MangoIV/dracuLad/graphics/marceline.png

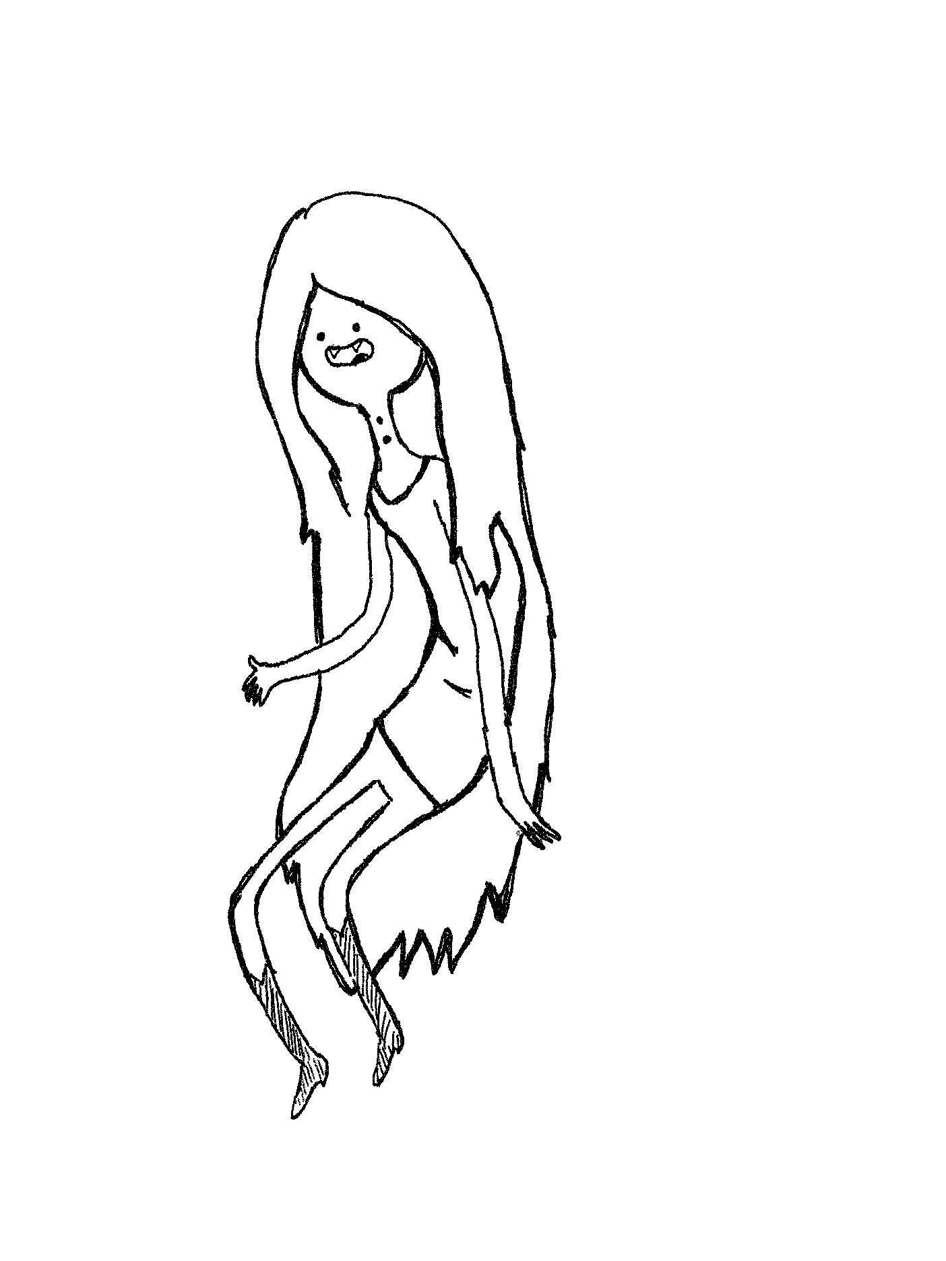
graphics/marceline.png
