MangoIV/dracuLad/pictures/rev2/acryli_no_caps_top.jpeg

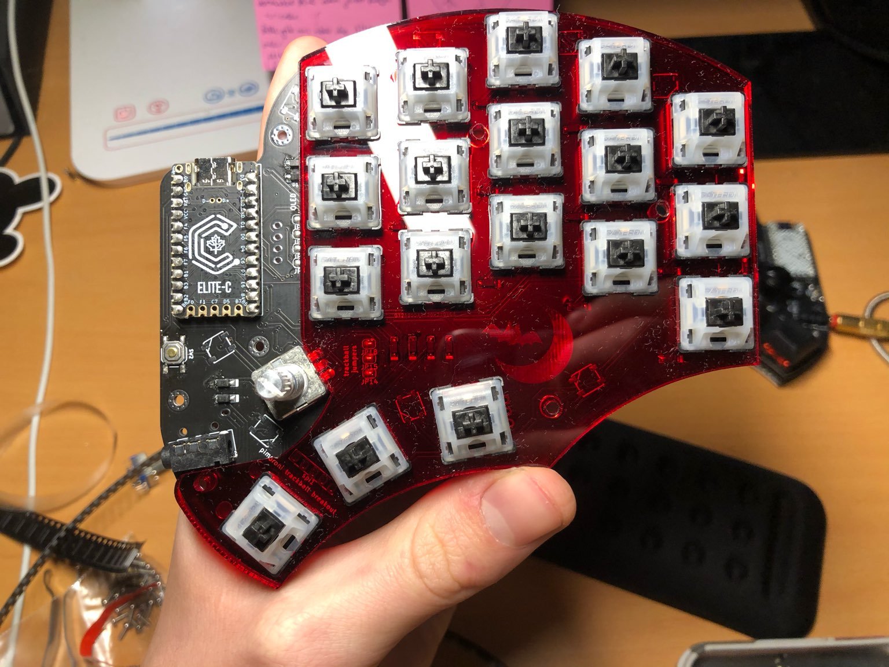
pictures/rev2/acryli_no_caps_top.jpeg
