MangoIV/dracuLad/pictures/rev2/acrylic_7mm_spacers.jpeg

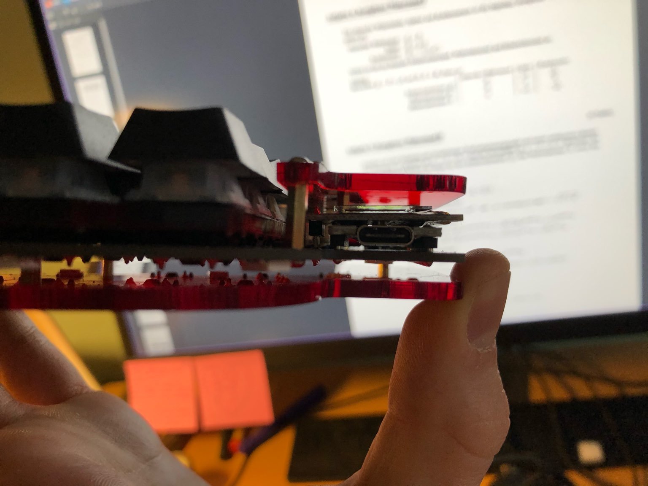
pictures/rev2/acrylic_7mm_spacers.jpeg
