MangoIV/dracuLad/pictures/rev2/acrylic_bottom_both_halves.jpeg

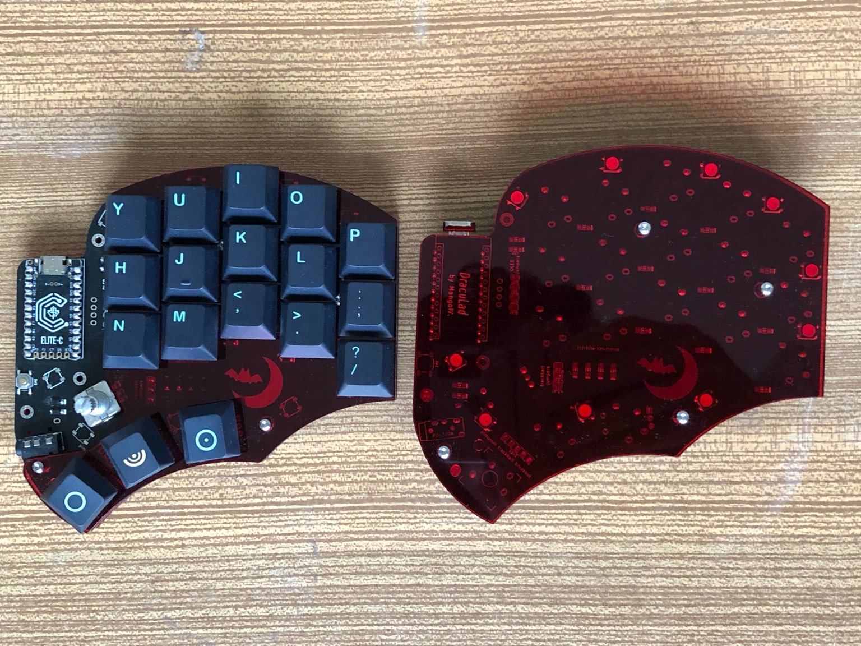
pictures/rev2/acrylic_bottom_both_halves.jpeg
