MangoIV/dracuLad/pictures/rev2/arylic_top_plate.jpeg

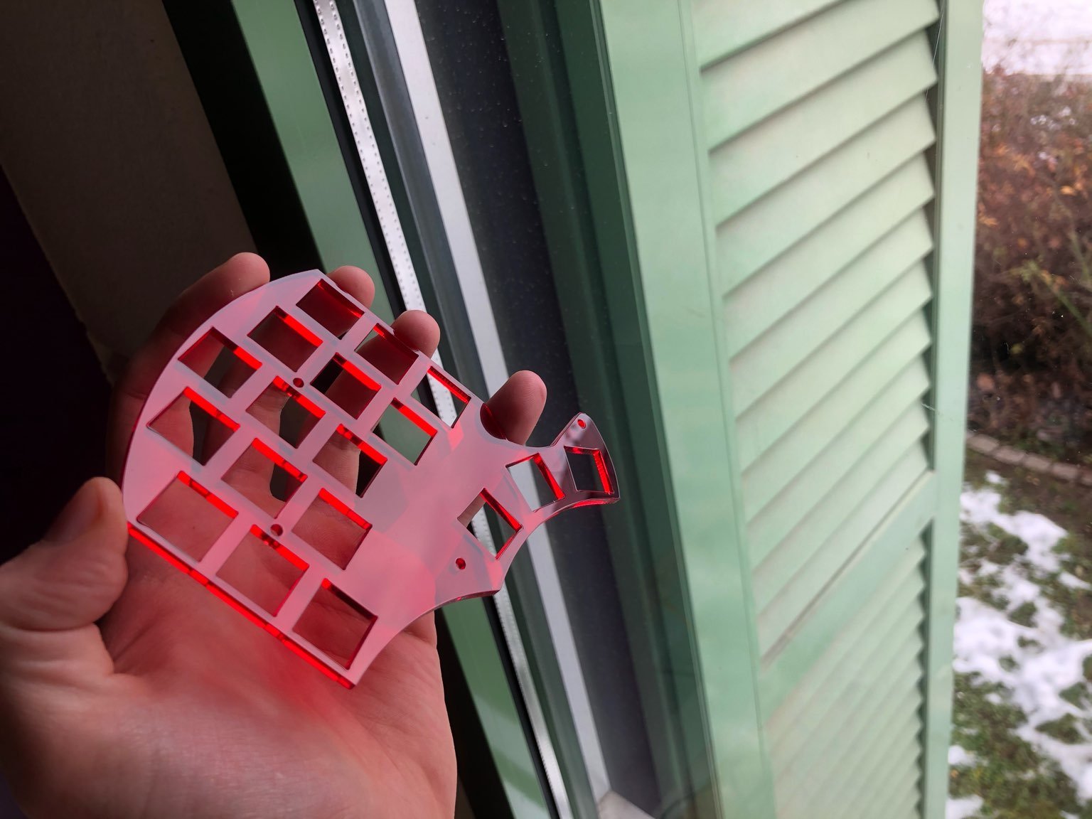
pictures/rev2/arylic_top_plate.jpeg
