MangoIV/dracuLad/pictures/rev2/fr4_glamour_puchi_c.jpeg

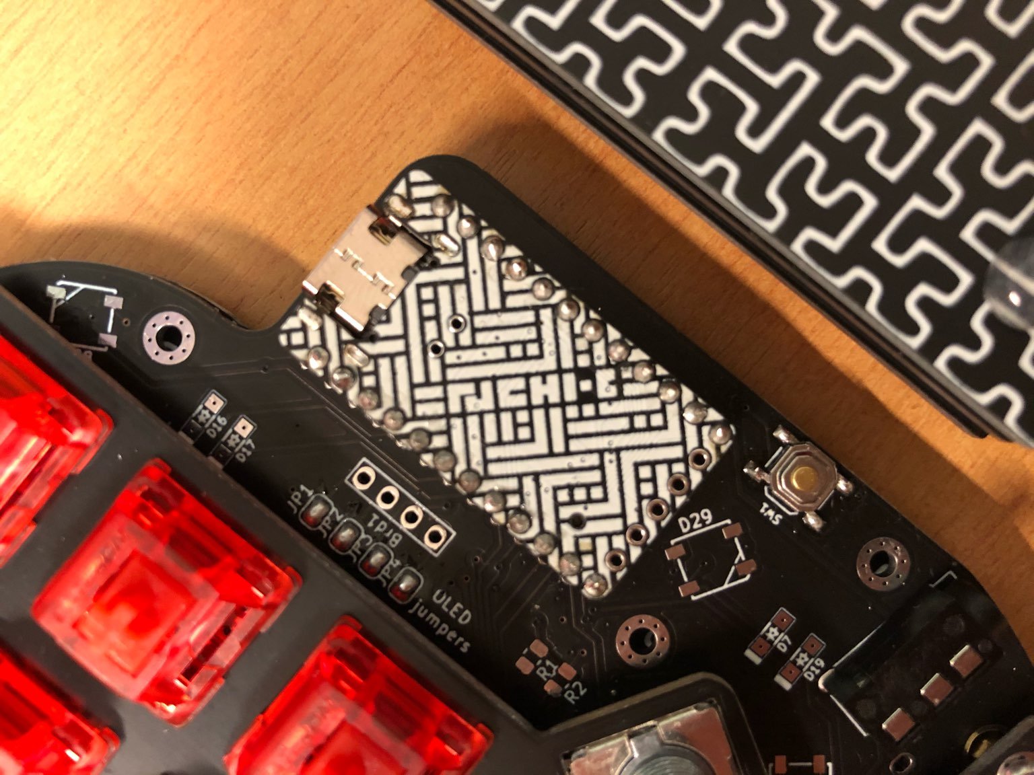
pictures/rev2/fr4_glamour_puchi_c.jpeg
