MangoIV/dracuLad/pictures/rev2/fr4_leds.jpeg

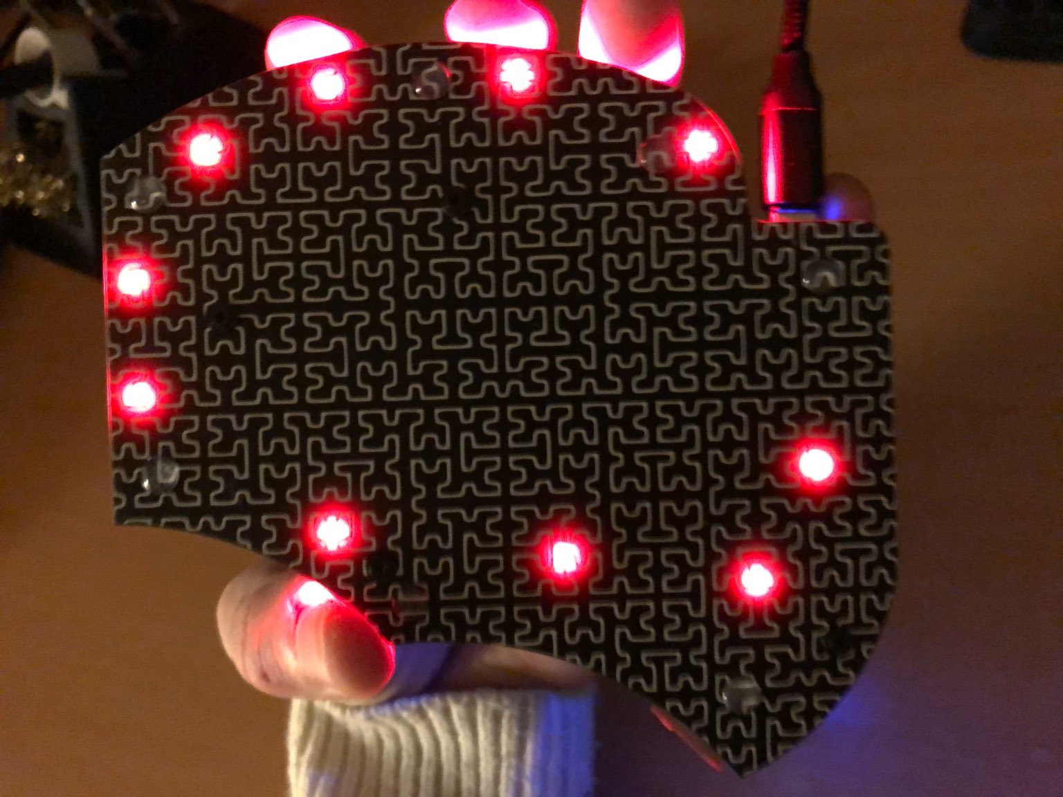
pictures/rev2/fr4_leds.jpeg
