MangoIV/dracuLad/pictures/rev2/fr4_mustard_packet.jpeg

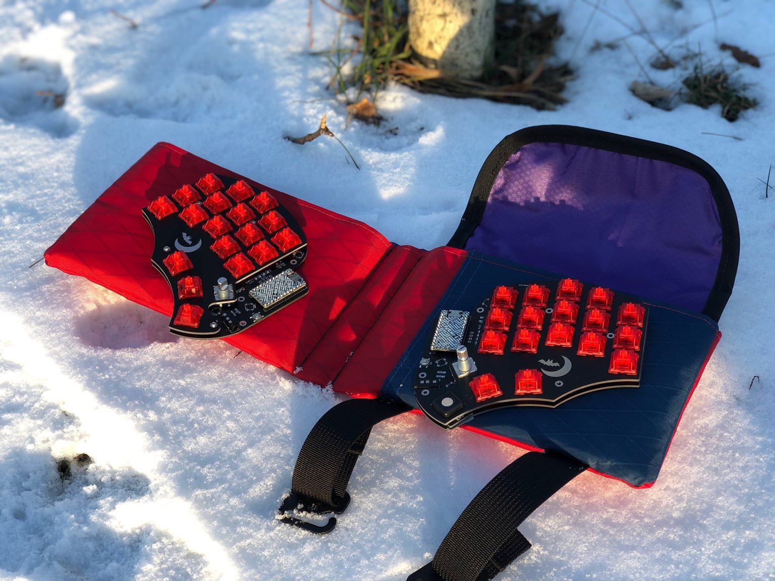
pictures/rev2/fr4_mustard_packet.jpeg
