MangoIV/dracuLad/pictures/rev2/rev2_trackball_right_side.jpeg

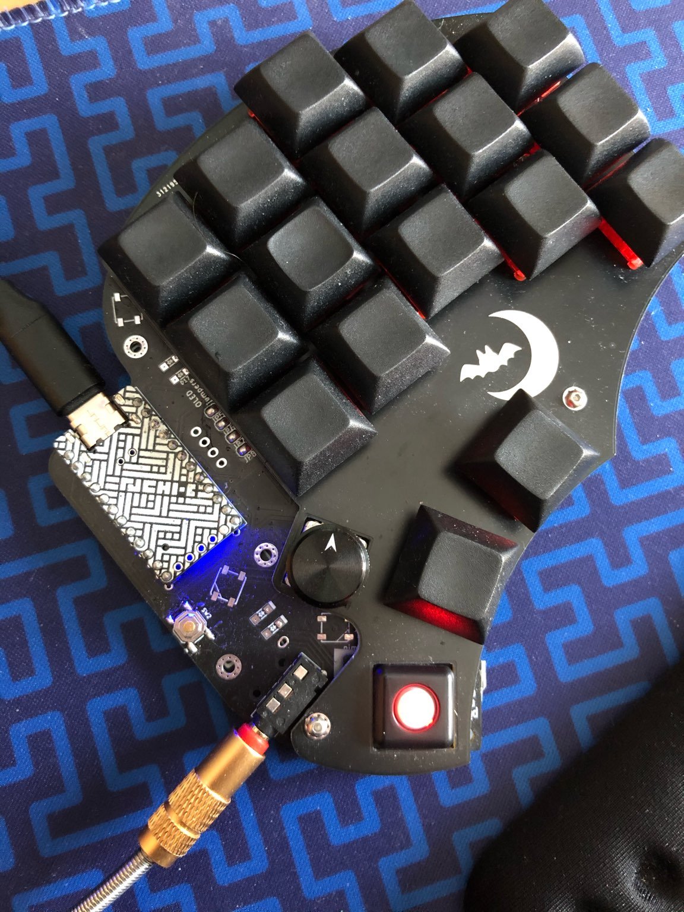
pictures/rev2/rev2_trackball_right_side.jpeg
