MangoIV/dracuLad/production_files/graphics/hilbert.png

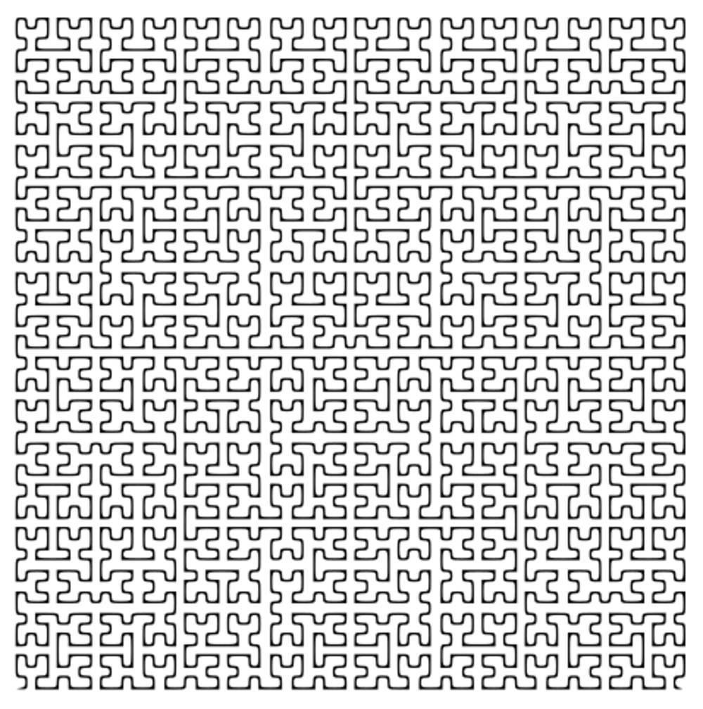
production_files/graphics/hilbert.png
