MangoIV/dracuLad/pictures/rev2/sadeks_build_2.jpg

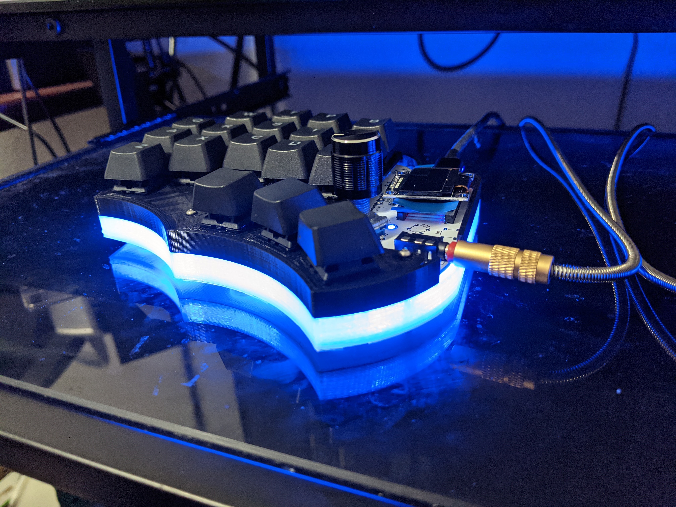
pictures/rev2/sadeks_build_2.jpg
